gregrob/publisher/include/version_cfg.h

#ifndef VERSION_CFG_H
#define VERSION_CFG_H

// Contents for the major version
#define VERSION_CONTENTS_MAJOR  "000"

// Contents for minor version
#define VERSION_CONTENTS_MINOR  "007"

// Contents for bugfix version
#define VERSION_CONTENTS_BUGFIX "007"

#endif
