gregrob/publisher/include/messages_tx_cfg.h

#ifndef MESSAGES_TX_CFG_H
#define MESSAGES_TX_CFG_H

// MQTT topic definition for module software
#define MESSAGES_TX_MQTT_TOPIC_MODULE_SOFTWARE    ("module software")

// MQTT topic definition for module nvm
#define MESSAGES_TX_MQTT_TOPIC_MODULE_NVM         ("module nvm")

// MQTT topic definition for module runtime
#define MESSAGES_TX_MQTT_TOPIC_MODULE_RUNTIME     ("module runtime")

// MQTT topic definition for module wifi
#define MESSAGES_TX_MQTT_TOPIC_MODULE_WIFI        ("module wifi")

// MQTT topic definition for alarm triggers
#define MESSAGES_TX_MQTT_TOPIC_ALARM_STATUS       ("alarm status")

// MQTT topic definition for alarm PIR
#define MESSAGES_TX_MQTT_TOPIC_ALARM_PIR          ("alarm pir")

// MQTT topic definition for alarm source
#define MESSAGES_TX_MQTT_TOPIC_ALARM_SOURCE       ("alarm source")

// MQTT topic definition for garage door status
#define MESSAGES_TX_MQTT_TOPIC_GARAGE_DOOR_STATUS ("garage door status")

#endif
